RobFro96/SimsonSpeed/ccs-project/lcd/digit.c

#include <stdint.h>
#include "lcd.h"

#include "digit.h"

#if 1
// Präprozessor-Anweisung für Folding

// Ziffern 6x8 für Legende der RPM-Anzeige (siehe gfx/digits_rpm.png)
static const uint8_t DIGIT_DATA_6x8[] = { 0x7e, 0xff, 0x81, 0x81, 0xff, 0x7e,
		0x82, 0xc1, 0xe1, 0xb1, 0x9f, 0x8e, 0x30, 0x2c, 0x23, 0xff, 0xff, 0x20,
		0x7c, 0xfe, 0x8b, 0x89, 0xf9, 0x70, 0x76, 0xff, 0x89, 0x89, 0xff, 0x76 };

// Ziffern 20x32 für die Anzeige der Geschwindigkeit (siehe gfx/digits_speed.png)
static const uint8_t DIGIT_DATA_20x32[] = { 0x0, 0xfe, 0xff, 0x0, 0xc0, 0xff,
		0xff, 0x3, 0xe0, 0xff, 0xff, 0xf, 0xf0, 0xff, 0xff, 0x1f, 0xf8, 0xff,
		0xff, 0x3f, 0xf8, 0xff, 0xff, 0x3f, 0xfc, 0xff, 0xff, 0x7f, 0xfc, 0x0,
		0x0, 0x7e, 0x7c, 0x0, 0x0, 0x7c, 0x7c, 0x0, 0x0, 0x7c, 0x7c, 0x0, 0x0,
		0x7c, 0x7c, 0x0, 0x0, 0x7c, 0xfc, 0x0, 0x0, 0x7e, 0xfc, 0xff, 0xff,
		0x7f, 0xf8, 0xff, 0xff, 0x3f, 0xf8, 0xff, 0xff, 0x3f, 0xf0, 0xff, 0xff,
		0x1f, 0xe0, 0xff, 0xff, 0xf, 0x80, 0xff, 0xff, 0x3, 0x0, 0xfe, 0xff,
		0x0, 0x0, 0x0, 0x0, 0x0, 0x0, 0x0, 0x0, 0x0, 0xc0, 0x7, 0x0, 0x0, 0xc0,
		0x7, 0x0, 0x0, 0xe0, 0x3, 0x0, 0x0, 0xe0, 0x3, 0x0, 0x0, 0xe0, 0x3, 0x0,
		0x0, 0xf0, 0x3, 0x0, 0x0, 0xf0, 0x1, 0x0, 0x0, 0xf0, 0xff, 0xff, 0x7f,
		0xf8, 0xff, 0xff, 0x7f, 0xf8, 0xff, 0xff, 0x7f, 0xf8, 0xff, 0xff, 0x7f,
		0xf8, 0xff, 0xff, 0x7f, 0xfc, 0xff, 0xff, 0x7f, 0xfc, 0xff, 0xff, 0x7f,
		0x0, 0x0, 0x0, 0x0, 0x0, 0x0, 0x0, 0x0, 0x0, 0x0, 0x0, 0x0, 0x0, 0x0,
		0x0, 0x0, 0x80, 0xf, 0x0, 0x7c, 0xc0, 0xf, 0x0, 0x7e, 0xe0, 0xf, 0x0,
		0x7f, 0xf0, 0xf, 0x80, 0x7f, 0xf8, 0xf, 0xc0, 0x7f, 0xf8, 0xf, 0xe0,
		0x7f, 0xfc, 0x1, 0xf0, 0x7f, 0xfc, 0x0, 0xf8, 0x7f, 0x7c, 0x0, 0xfc,
		0x7f, 0x7c, 0x0, 0xfe, 0x7d, 0x7c, 0x0, 0xff, 0x7c, 0xfc, 0xc0, 0x7f,
		0x7c, 0xfc, 0xf1, 0x3f, 0x7c, 0xfc, 0xff, 0x1f, 0x7c, 0xf8, 0xff, 0xf,
		0x7c, 0xf8, 0xff, 0x7, 0x7c, 0xf0, 0xff, 0x1, 0x7c, 0xe0, 0xff, 0x0,
		0x7c, 0xc0, 0x3f, 0x0, 0x7c, 0x0, 0x6, 0x0, 0x7c, 0xc0, 0x1, 0x80, 0x7,
		0xe0, 0x1, 0x80, 0xf, 0xf0, 0x1, 0x80, 0x1f, 0xf8, 0x1, 0x80, 0x3f,
		0xf8, 0x1, 0x80, 0x3f, 0xf8, 0x1, 0x80, 0x3f, 0xfc, 0xe0, 0x3, 0x7f,
		0xfc, 0xe0, 0x3, 0x7e, 0x7c, 0xe0, 0x3, 0x7c, 0x7c, 0xe0, 0x3, 0x7c,
		0x7c, 0xe0, 0x3, 0x7c, 0x7c, 0xe0, 0x3, 0x7c, 0xfc, 0xf0, 0x7, 0x7e,
		0xfc, 0xff, 0xff, 0x3f, 0xf8, 0xff, 0xff, 0x3f, 0xf8, 0xff, 0xff, 0x3f,
		0xf0, 0x7f, 0xff, 0x1f, 0xf0, 0x3f, 0xfe, 0xf, 0xc0, 0x1f, 0xfe, 0x7,
		0x0, 0x7, 0xf8, 0x3, 0x0, 0x0, 0xf8, 0x1, 0x0, 0x0, 0xfe, 0x1, 0x0, 0x0,
		0xff, 0x1, 0x0, 0xc0, 0xff, 0x1, 0x0, 0xe0, 0xff, 0x1, 0x0, 0xf8, 0xff,
		0x1, 0x0, 0xfe, 0xf7, 0x1, 0x0, 0xff, 0xf1, 0x1, 0xc0, 0x7f, 0xf0, 0x1,
		0xf0, 0x1f, 0xf0, 0x1, 0xf8, 0xf, 0xf0, 0x1, 0xfc, 0xff, 0xff, 0x7f,
		0xfc, 0xff, 0xff, 0x7f, 0xfc, 0xff, 0xff, 0x7f, 0xfc, 0xff, 0xff, 0x7f,
		0xfc, 0xff, 0xff, 0x7f, 0xfc, 0xff, 0xff, 0x7f, 0xfc, 0xff, 0xff, 0x7f,
		0x0, 0x0, 0xf0, 0x1, 0x0, 0x0, 0xf0, 0x1, 0x0, 0x0, 0x80, 0x3, 0x80,
		0xff, 0x81, 0x7, 0xfc, 0xff, 0x83, 0xf, 0xfc, 0xff, 0x83, 0x1f, 0xfc,
		0xff, 0x83, 0x3f, 0xfc, 0xff, 0x83, 0x3f, 0xfc, 0xff, 0x83, 0x7f, 0xfc,
		0xe0, 0x1, 0x7e, 0x7c, 0xf0, 0x1, 0x7c, 0x7c, 0xf0, 0x1, 0x7c, 0x7c,
		0xf0, 0x1, 0x7c, 0x7c, 0xf0, 0x1, 0x7c, 0x7c, 0xf0, 0x3, 0x7e, 0x7c,
		0xf0, 0xff, 0x7f, 0x7c, 0xf0, 0xff, 0x3f, 0x7c, 0xe0, 0xff, 0x3f, 0x7c,
		0xe0, 0xff, 0x1f, 0x7c, 0xc0, 0xff, 0xf, 0x7c, 0x80, 0xff, 0x7, 0x0,
		0x0, 0xfe, 0x1, 0x0, 0xf0, 0xff, 0x0, 0x0, 0xfc, 0xff, 0x3, 0x0, 0xff,
		0xff, 0xf, 0x80, 0xff, 0xff, 0x1f, 0xc0, 0xff, 0xff, 0x1f, 0xe0, 0xff,
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
#endif

/**
 * Zeichnen einer 6x8 Ziffer, es können nur geradzahlige Ziffern angezeigt werden
 *
 * @param x			X-Position
 * @param y_page	Y-Page
 * @param digit		Index der geradzahligen Ziffer (digit=4 -> Anzeige: 8)
 */
void digit_draw_6x8(uint8_t x, uint8_t y_page, uint8_t digit) {
	const uint8_t *pt = &(DIGIT_DATA_6x8[6 * digit]);

	for (uint8_t i = 0; i < 6; i++) {
		lcd_set_pixels(x + i, y_page, *pt);
		pt++;
	}
}

/**
 * Zeichnen einer 20x32 Ziffer
 *
 * @param x			X-Position
 * @param y_page	Y-Page
 * @param digit		Ziffer
 */
void digit_draw_20x32(uint8_t x, uint8_t y_page, uint8_t digit) {
	const uint8_t *pt = &(DIGIT_DATA_20x32[20 * 4 * digit]);

	for (uint8_t i = 0; i < 20; i++) {
		for (uint8_t y = 0; y < 4; y++) {
			lcd_set_pixels(x + i, y_page + y, *pt);
			pt++;
		}
	}
}

/**
 * Löschen des Bereiches einer 20x32 Ziffer
 *
 * @param x			X-Position
 * @param y_page	Y-Page
 */
void digit_clear_20x32(uint8_t x, uint8_t y_page) {
	for (uint8_t i = 0; i < 20; i++) {
		for (uint8_t y = 0; y < 4; y++) {
			lcd_set_pixels(x + i, y_page + y, 0);
		}
	}
}
