RobFro96/SimsonSpeed/ccs-project/lcd/digit.h

#ifndef DIGIT_H_
#define DIGIT_H_

void digit_draw_6x8(uint8_t x, uint8_t y_page, uint8_t digit);
void digit_draw_20x32(uint8_t x, uint8_t y_page, uint8_t digit);
void digit_clear_20x32(uint8_t x, uint8_t y_page);

#endif /* DIGIT_H_ */
